samuelclay/turntouch-remote/remote eagle/eagleUp/eagleUp_remote_board_top.png

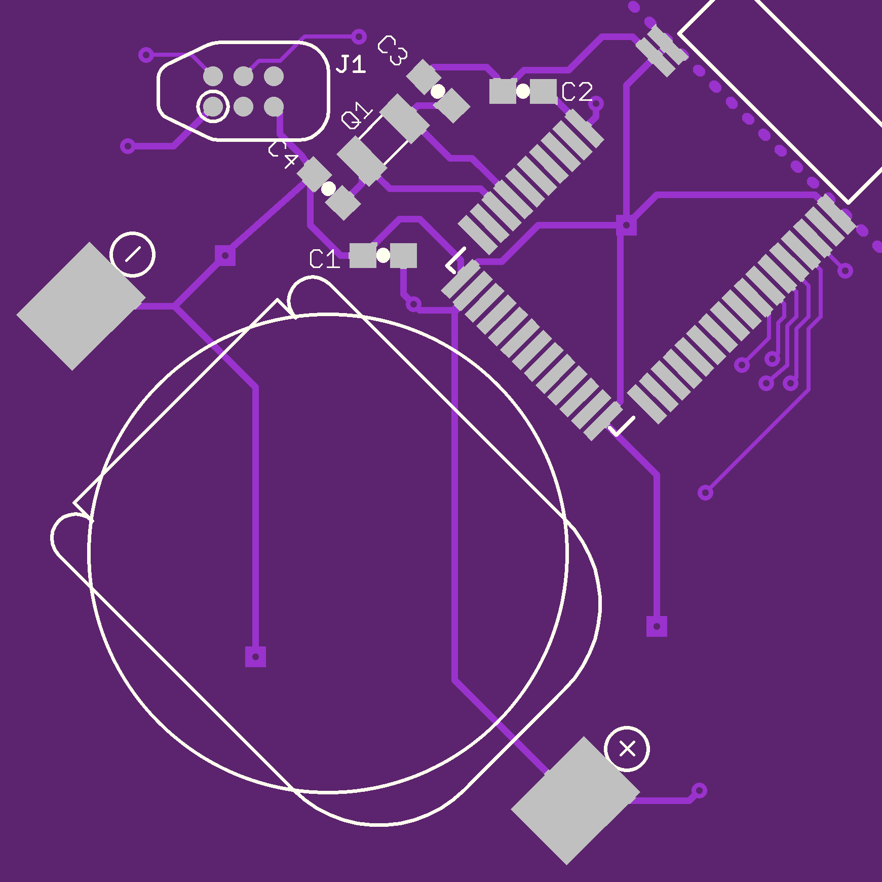
remote eagle/eagleUp/eagleUp_remote_board_top.png
