samuelclay/turntouch-remote/remote eagle/eagleUp/rev38 eagleUp_turntouch-remote-master_board_top.png

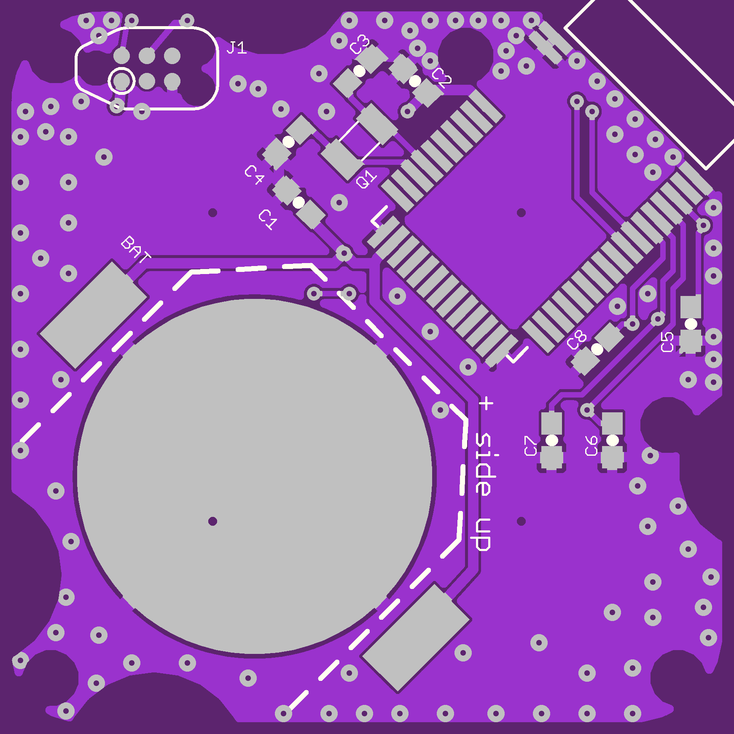
remote eagle/eagleUp/rev38 eagleUp_turntouch-remote-master_board_top.png
