samuelclay/turntouch-remote/remote eagle/eagleUp/rev40 eagleUp_turntouch-remote-master_board_bottom.png

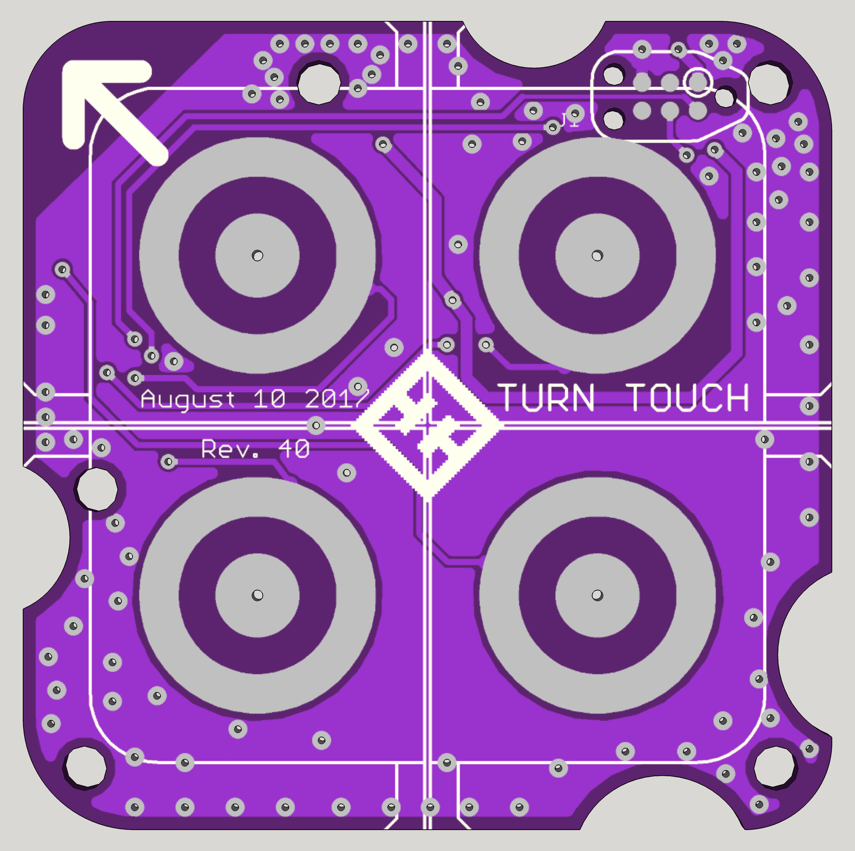
remote eagle/eagleUp/rev40 eagleUp_turntouch-remote-master_board_bottom.png
