samuelclay/turntouch-remote/remote eagle/turntouch-remote-master-pcb-info.png

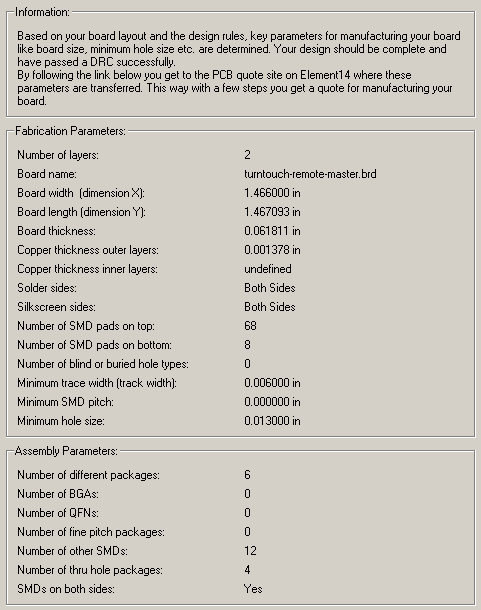
remote eagle/turntouch-remote-master-pcb-info.png
