samuelclay/turntouch-remote/remote eagle/turntuch-pcb.png

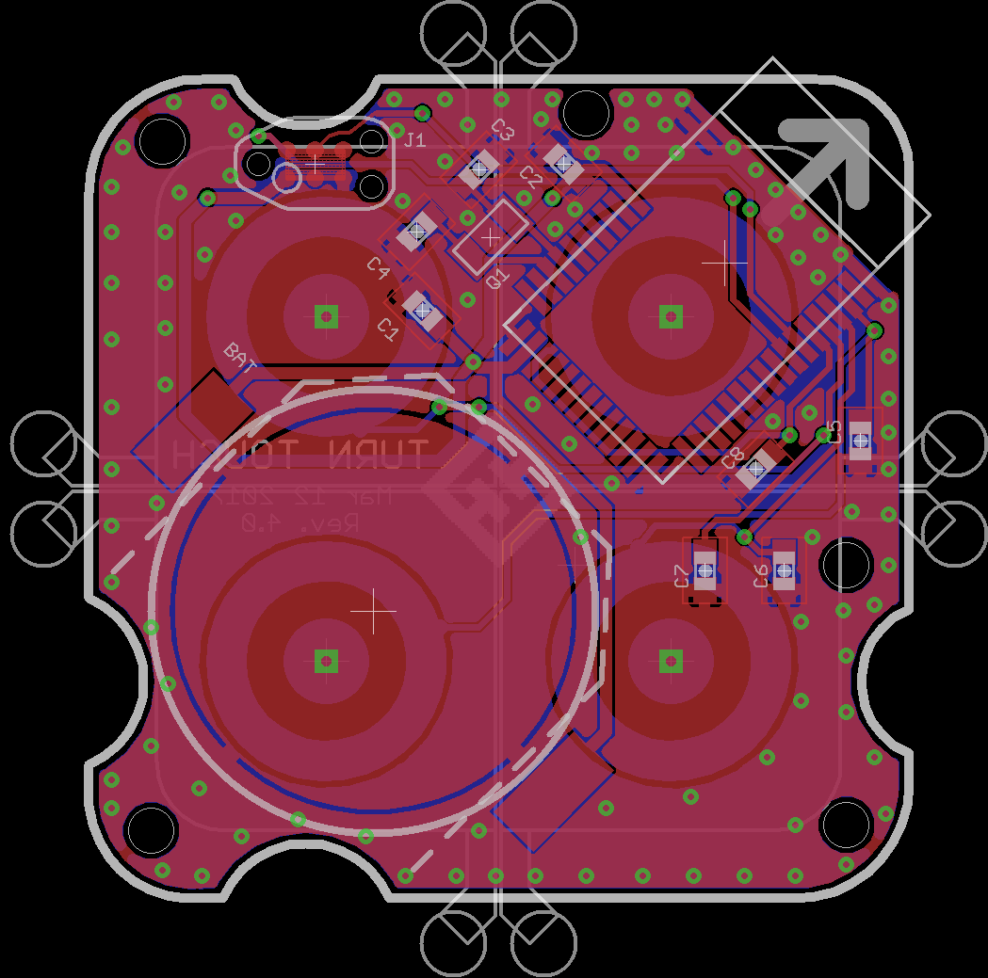
remote eagle/turntuch-pcb.png
