samuelclay/turntouch-remote/enclosure/rhino/remote.stp

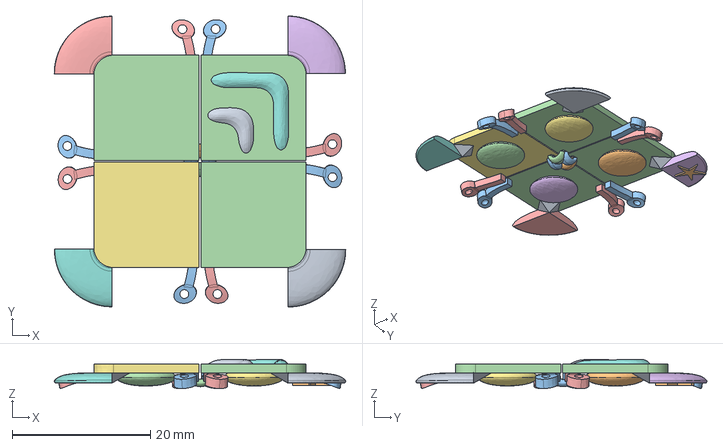
[picture p26: CAD file, 2015-05-19]
enclosure/rhino/remote.stp
42.2 x 42.1 x 4.23 mm
