samuelclay/turntouch-remote/enclosure/solidworks/Remote Bottom.sldprt

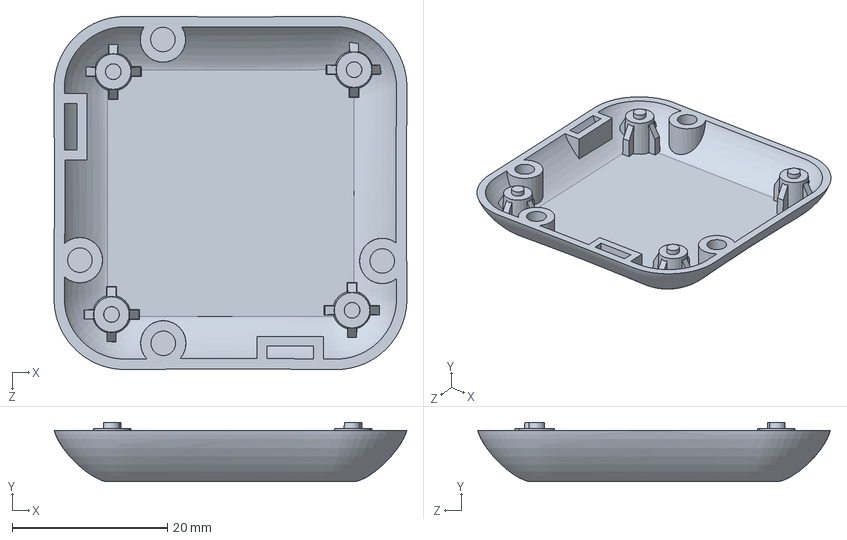
[picture p28: CAD file, 2015-06-07]
enclosure/solidworks/Remote Bottom.sldprt
45.5 x 7.62 x 45.5 mm
