samuelclay/turntouch-remote/enclosure/rhino/bottom.stp

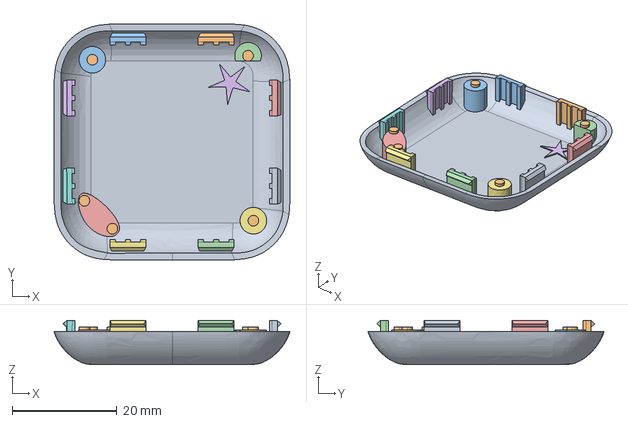
[picture p29: CAD file, 2015-05-19]
enclosure/rhino/bottom.stp
45.1 x 45.1 x 8.46 mm
