samuelclay/turntouch-remote/enclosure/solidworks/Remote Shell.SLDPRT

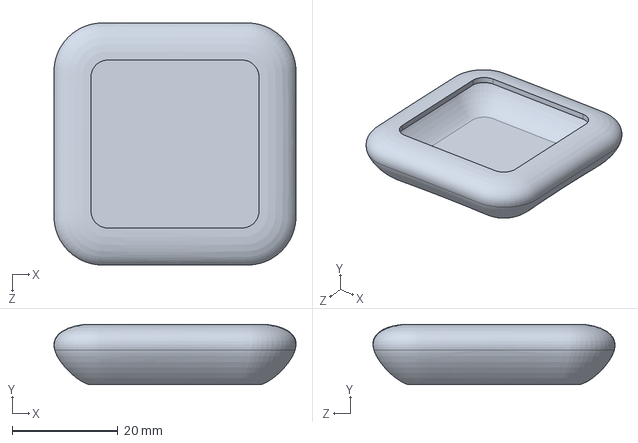
[picture p30: CAD file, 2015-06-06]
enclosure/solidworks/Remote Shell.SLDPRT
45.7 x 11.4 x 45.7 mm
