samuelclay/turntouch-remote/enclosure/rhino/top.stp

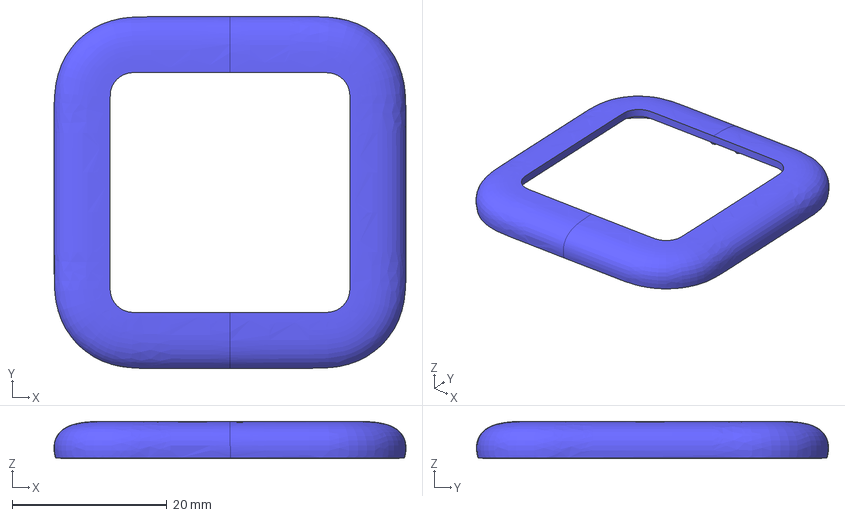
[picture p31: CAD file, 2015-05-19]
enclosure/rhino/top.stp
45.4 x 45.4 x 4.84 mm
