samuelclay/turntouch-remote/doc/Capture - debug connectors on nRF51 DK.JPG

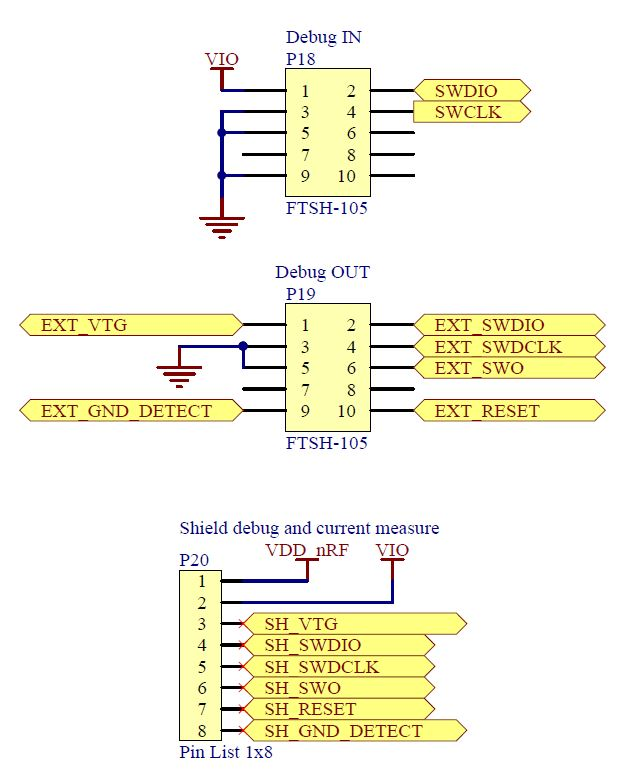
doc/Capture - debug connectors on nRF51 DK.JPG
