samuelclay/turntouch-remote/ble_peripheral/app_9.0/rtt.h

/* Copyright 2015 Turn Touch. All rights reserved.
 * 
 * Header for RTT debugging.
 * 
 */

#include "RTT/SEGGER_RTT.h"

void rtt_print(unsigned BufferIndex, const char * sFormat, ...);
void rtt_log(const char * str, ...);
